bagelboy137/Bear-Necessities-/Mac Mini Setup/tools/cad-product-agent/production/ten-modules/visual/renders/BN-M06-alpha.png

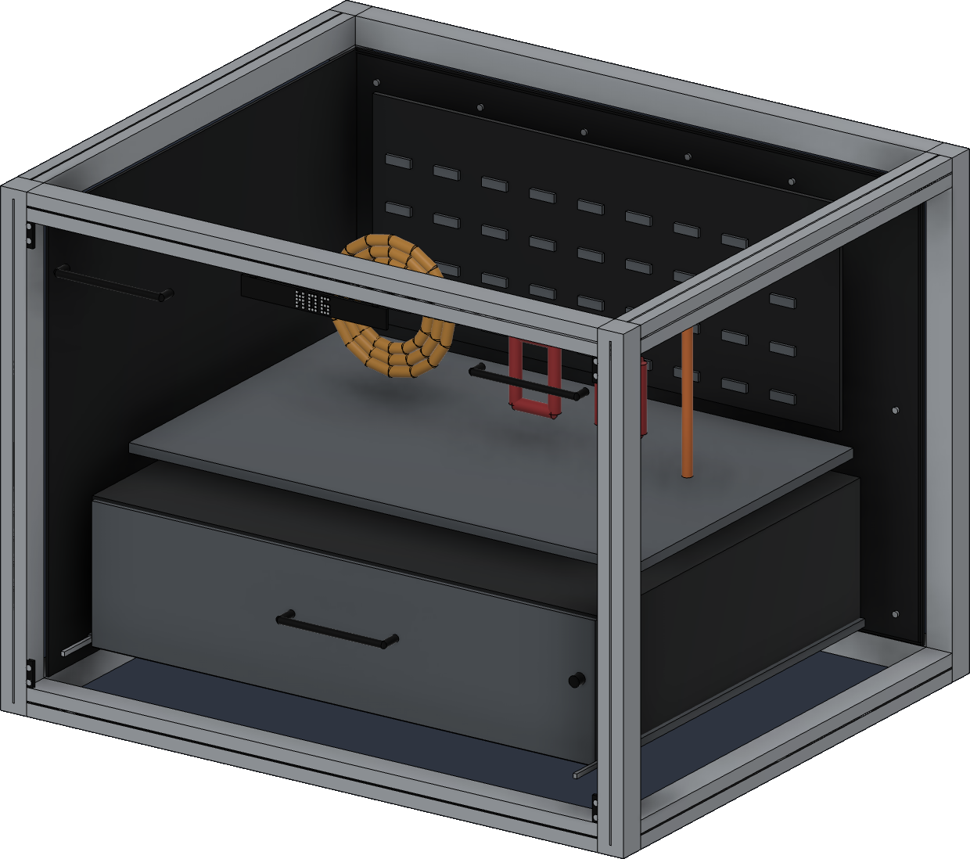
Mac Mini Setup/tools/cad-product-agent/production/ten-modules/visual/renders/BN-M06-alpha.png
