bagelboy137/Bear-Necessities-/Mac Mini Setup/tools/cad-product-agent/production/ten-modules/iterations/runs/design/design-06.attempt-1.raw.txt

```json
{
  "cycle_id": "design-06",
  "reviews": [
    {
      "module_id": "BN-M01",
      "verdict": "RETAIN",
      "proposal": "Retain the current design.",
      "rationale": "The module clearly communicates a secure stowed state with visible latches and restraints, as well as its deployed state with exposed burners and controls.",
      "evidence_ids": ["CURRENT-CAD", "FRAME-CONSTRAINTS"],
      "acceptance_check": "Check for visible latches and restraints in the stowed state.",
      "risk": "None"
    },
    {
      "module_id": "BN-M02",
      "verdict": "RETAIN",
      "proposal": "Retain the current design.",
      "rationale": "The module clearly communicates a secure stowed state with visible latches and restraints, as well as its deployed state with open drawers.",
      "evidence_ids": ["CURRENT-CAD", "FRAME-CONSTRAINTS"],
      "acceptance_check": "Check for visible latches and restraints in the stowed state.",
      "risk": "None"
    },
    {
      "module_id": "BN-M03",
      "verdict": "RETAIN",
      "proposal": "Retain the current design.",
      "rationale": "The module clearly communicates a secure stowed state with visible latches and restraints, as well as its deployed state with an open fridge lid.",
      "evidence_ids": ["CURRENT-CAD", "FRAME-CONSTRAINTS"],
      "acceptance_check": "Check for visible latches and restraints in the stowed state.",
      "risk": "None"
    },
    {
      "module_id": "BN-M04",
      "verdict": "RETAIN",
      "proposal": "Retain the current design.",
      "rationale": "The module clearly communicates a secure stowed state with visible latches and restraints, as well as its deployed state with an open basin.",
      "evidence_ids": ["CURRENT-CAD", "FRAME-CONSTRAINTS"],
      "acceptance_check": "Check for visible latches and restraints in the stowed state.",
      "risk": "None"
    },
    {
      "module_id": "BN-M05",
      "verdict": "RETAIN",
      "proposal": "Retain the current design.",
      "rationale": "The module clearly communicates a secure stowed state with visible latches and restraints, as well as its deployed state with an open spigot.",
      "evidence_ids": ["CURRENT-CAD", "FRAME-CONSTRAINTS"],
      "acceptance_check": "Check for visible latches and restraints in the stowed state.",
      "risk": "None"
    },
    {
      "module_id": "BN-M06",
      "verdict": "RETAIN",
      "proposal": "Retain the current design.",
      "rationale": "The module clearly communicates a secure stowed state with visible latches and restraints, as well as its deployed state with an open drawer.",
      "evidence_ids": ["CURRENT-CAD", "FRAME-CONSTRAINTS"],
      "acceptance_check": "Check for visible latches and restraints in the stowed state.",
      "risk": "None"
    },
    {
      "module_id": "BN-M07",
      "verdict": "RETAIN",
      "proposal": "Retain the current design.",
      "rationale": "The module clearly communicates a secure stowed state with visible latches and restraints, as well as its deployed state with open ports.",
      "evidence_ids": ["CURRENT-CAD", "FRAME-CONSTRAINTS"],
      "acceptance_check": "Check for visible latches and restraints in the stowed state.",
      "risk": "None"
    },
    {
      "module_id": "BN-M08",
      "verdict": "RETAIN",
      "proposal": "Retain the current design.",
      "rationale": "The module clearly communicates a secure stowed state with visible latches and restraints, as well as its deployed state with an open shower head.",
      "evidence_ids": ["CURRENT-CAD", "FRAME-CONSTRAINTS"],
      "acceptance_check": "Check for visible latches and restraints in the stowed state.",
      "risk": "None"
    },
    {
      "module_id": "BN-M09",
      "verdict": "RETAIN",
      "proposal": "Retain the current design.",
      "rationale": "The module clearly communicates a secure stowed state with visible latches and restraints, as well as its deployed state with an open worktop.",
      "evidence_ids": ["CURRENT-CAD", "FRAME-CONSTRAINTS"],
      "acceptance_check": "Check for visible latches and restraints in the stowed state.",
      "risk": "None"
    },
    {
      "module_id": "BN-M10",
      "verdict": "RETAIN",
      "proposal": "Retain the current design.",
      "rationale": "The module clearly communicates a secure stowed state with visible latches and restraints, as well as its deployed state with open furniture bags.",
      "evidence_ids": ["CURRENT-CAD", "FRAME-CONSTRAINTS"],
      "acceptance_check": "Check for visible latches and restraints in the stowed state.",
      "risk": "None"
    }
  ]
}
```
