bagelboy137/Bear-Necessities-/Mac Mini Setup/tools/cad-product-agent/production/ten-modules/iterations/runs/design/design-09.attempt-1.raw.txt

```json
{
  "cycle_id": "design-09",
  "reviews": [
    {
      "module_id": "BN-M01",
      "verdict": "RETAIN",
      "proposal": "Retain the current design.",
      "rationale": "The module maintains a distinct function as part of the silver-extrusion, dark-panel family.",
      "evidence_ids": ["CURRENT-CAD", "FRAME-CONSTRAINTS"],
      "acceptance_check": "Verify that the module adheres to the visual language constraints.",
      "risk": "None"
    },
    {
      "module_id": "BN-M02",
      "verdict": "RETAIN",
      "proposal": "Retain the current design.",
      "rationale": "The module maintains a distinct function as part of the silver-extrusion, dark-panel family.",
      "evidence_ids": ["CURRENT-CAD", "FRAME-CONSTRAINTS"],
      "acceptance_check": "Verify that the module adheres to the visual language constraints.",
      "risk": "None"
    },
    {
      "module_id": "BN-M03",
      "verdict": "RETAIN",
      "proposal": "Retain the current design.",
      "rationale": "The module maintains a distinct function as part of the silver-extrusion, dark-panel family.",
      "evidence_ids": ["CURRENT-CAD", "FRAME-CONSTRAINTS"],
      "acceptance_check": "Verify that the module adheres to the visual language constraints.",
      "risk": "None"
    },
    {
      "module_id": "BN-M04",
      "verdict": "RETAIN",
      "proposal": "Retain the current design.",
      "rationale": "The module maintains a distinct function as part of the silver-extrusion, dark-panel family.",
      "evidence_ids": ["CURRENT-CAD", "FRAME-CONSTRAINTS"],
      "acceptance_check": "Verify that the module adheres to the visual language constraints.",
      "risk": "None"
    },
    {
      "module_id": "BN-M05",
      "verdict": "RETAIN",
      "proposal": "Retain the current design.",
      "rationale": "The module maintains a distinct function as part of the silver-extrusion, dark-panel family.",
      "evidence_ids": ["CURRENT-CAD", "FRAME-CONSTRAINTS"],
      "acceptance_check": "Verify that the module adheres to the visual language constraints.",
      "risk": "None"
    },
    {
      "module_id": "BN-M06",
      "verdict": "RETAIN",
      "proposal": "Retain the current design.",
      "rationale": "The module maintains a distinct function as part of the silver-extrusion, dark-panel family.",
      "evidence_ids": ["CURRENT-CAD", "FRAME-CONSTRAINTS"],
      "acceptance_check": "Verify that the module adheres to the visual language constraints.",
      "risk": "None"
    },
    {
      "module_id": "BN-M07",
      "verdict": "RETAIN",
      "proposal": "Retain the current design.",
      "rationale": "The module maintains a distinct function as part of the silver-extrusion, dark-panel family.",
      "evidence_ids": ["CURRENT-CAD", "FRAME-CONSTRAINTS"],
      "acceptance_check": "Verify that the module adheres to the visual language constraints.",
      "risk": "None"
    },
    {
      "module_id": "BN-M08",
      "verdict": "RETAIN",
      "proposal": "Retain the current design.",
      "rationale": "The module maintains a distinct function as part of the silver-extrusion, dark-panel family.",
      "evidence_ids": ["CURRENT-CAD", "FRAME-CONSTRAINTS"],
      "acceptance_check": "Verify that the module adheres to the visual language constraints.",
      "risk": "None"
    },
    {
      "module_id": "BN-M09",
      "verdict": "RETAIN",
      "proposal": "Retain the current design.",
      "rationale": "The module maintains a distinct function as part of the silver-extrusion, dark-panel family.",
      "evidence_ids": ["CURRENT-CAD", "FRAME-CONSTRAINTS"],
      "acceptance_check": "Verify that the module adheres to the visual language constraints.",
      "risk": "None"
    },
    {
      "module_id": "BN-M10",
      "verdict": "RETAIN",
      "proposal": "Retain the current design.",
      "rationale": "The module maintains a distinct function as part of the silver-extrusion, dark-panel family.",
      "evidence_ids": ["CURRENT-CAD", "FRAME-CONSTRAINTS"],
      "acceptance_check": "Verify that the module adheres to the visual language constraints.",
      "risk": "None"
    }
  ]
}
```
