bagelboy137/Bear-Necessities-/Fusion CAD Agent/evals/tasks/01-plate.md

Write a Fusion Python API script that creates a 100 x 60 x 6 mm rectangular plate.
