bagelboy137/Bear-Necessities-/Fusion CAD Agent/evals/tasks/02-holes.md

Write a Fusion Python API script that creates a 100 x 60 x 6 mm rectangular plate, then adds four 8 mm through-holes, one 10 mm in from each corner measured to the hole centre.
