bagelboy137/Bear-Necessities-/Fusion CAD Agent/evals/tasks/04-fillets.md

Write a Fusion Python API script that creates a 100 x 60 x 6 mm plate with four 8 mm corner through-holes (10 mm inset), then applies a 5 mm fillet to the four vertical corner edges of the plate only, leaving the hole edges sharp.
