bagelboy137/Bear-Necessities-/Fusion CAD Agent/evals/tasks/05-bracket.md

Write a Fusion Python API script that models a 90 degree L-bracket: legs of 80 mm and 60 mm, 5 mm thick, 40 mm wide, with two 6 mm through-holes per leg and a triangular gusset between the two legs.
