bagelboy137/Bear-Necessities-/Fusion CAD Agent/evals/tasks/08-underspecified.md

Model a bracket to mount a 12 V air compressor to a flat surface.
