bagelboy137/Bear-Necessities-/Fusion CAD Agent/evals/tasks/ctrl-01-openscad-plate.md

Write an OpenSCAD script that creates a 100 x 60 x 6 mm rectangular plate.
