bagelboy137/Bear-Necessities-/Bear Necessities/bear-necessities-social-preview.png

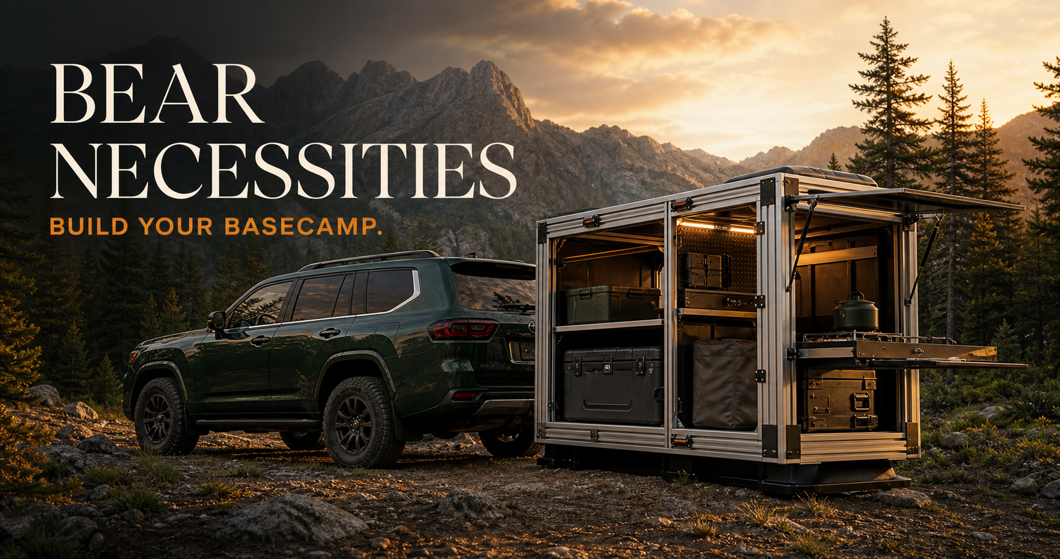
Bear Necessities/bear-necessities-social-preview.png
