bagelboy137/Bear-Necessities-/Bear Necessities/product/drawings/C-01-anchor-plate-FLAT.png

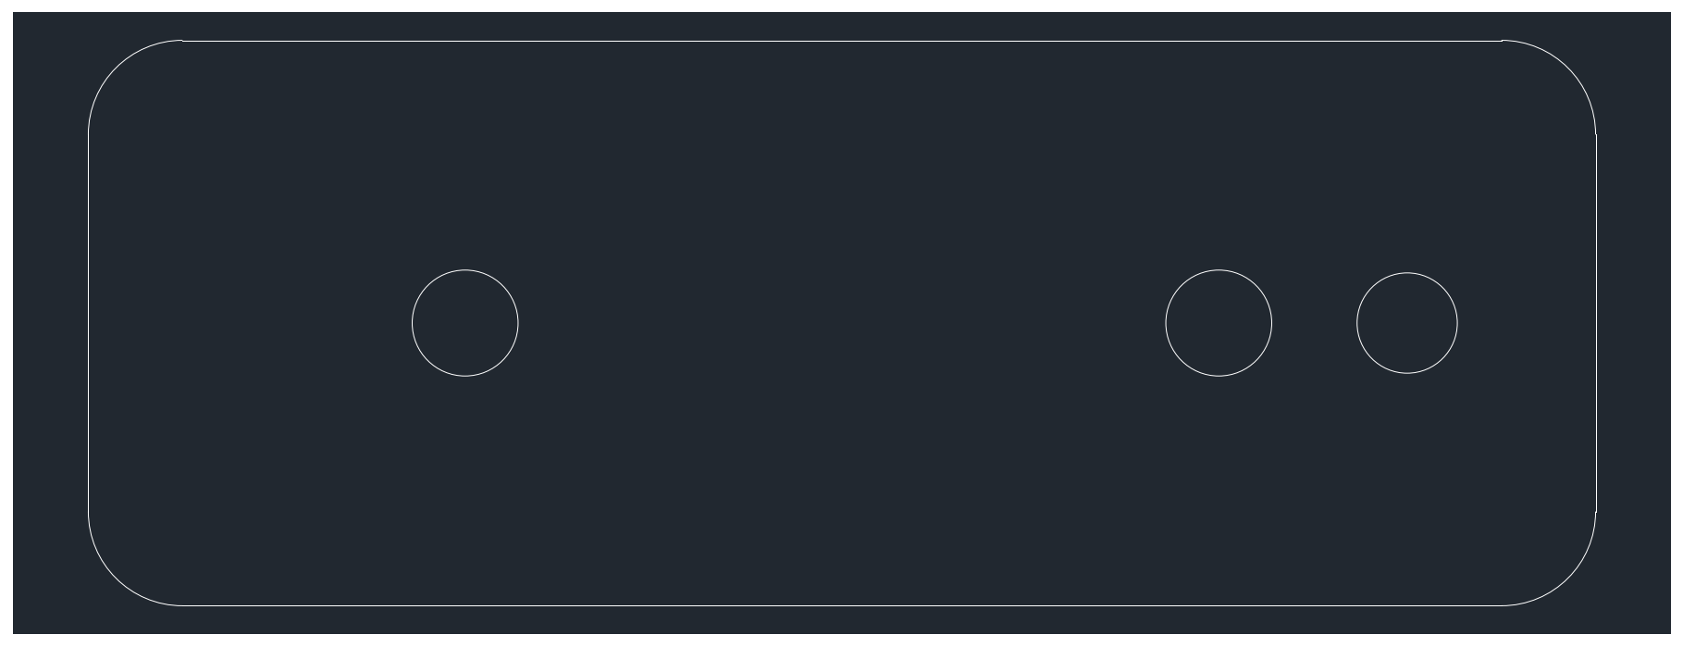
Bear Necessities/product/drawings/C-01-anchor-plate-FLAT.png
