bagelboy137/Bear-Necessities-/Bear Necessities/product/marketing/configurations/basecamp.png

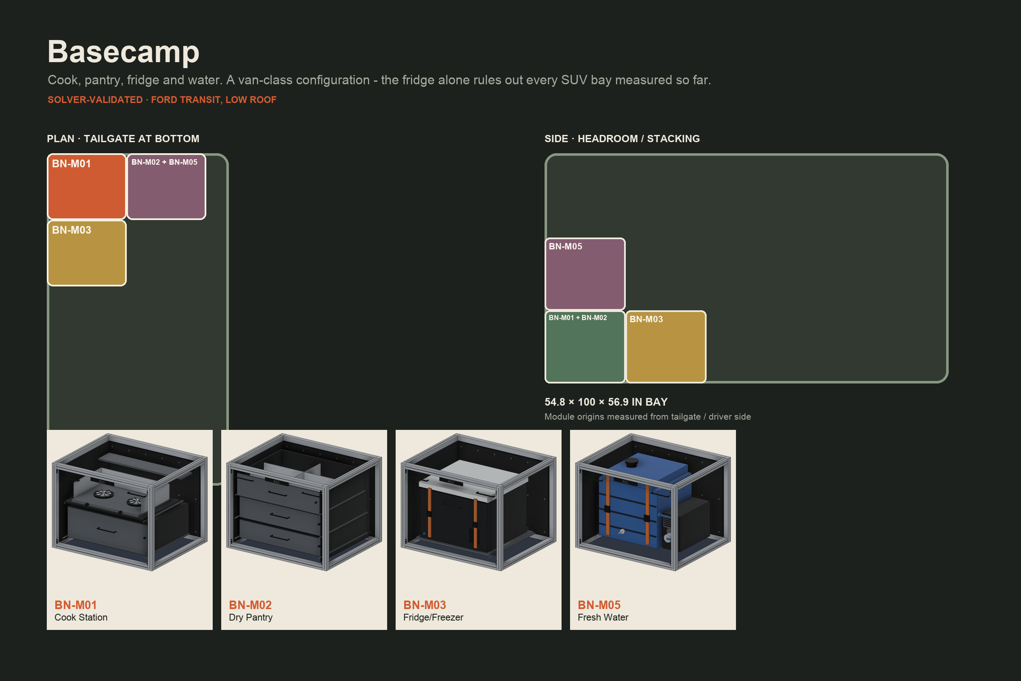
Bear Necessities/product/marketing/configurations/basecamp.png
