bagelboy137/Bear-Necessities-/Bear Necessities/product/marketing/configurations/expedition.png

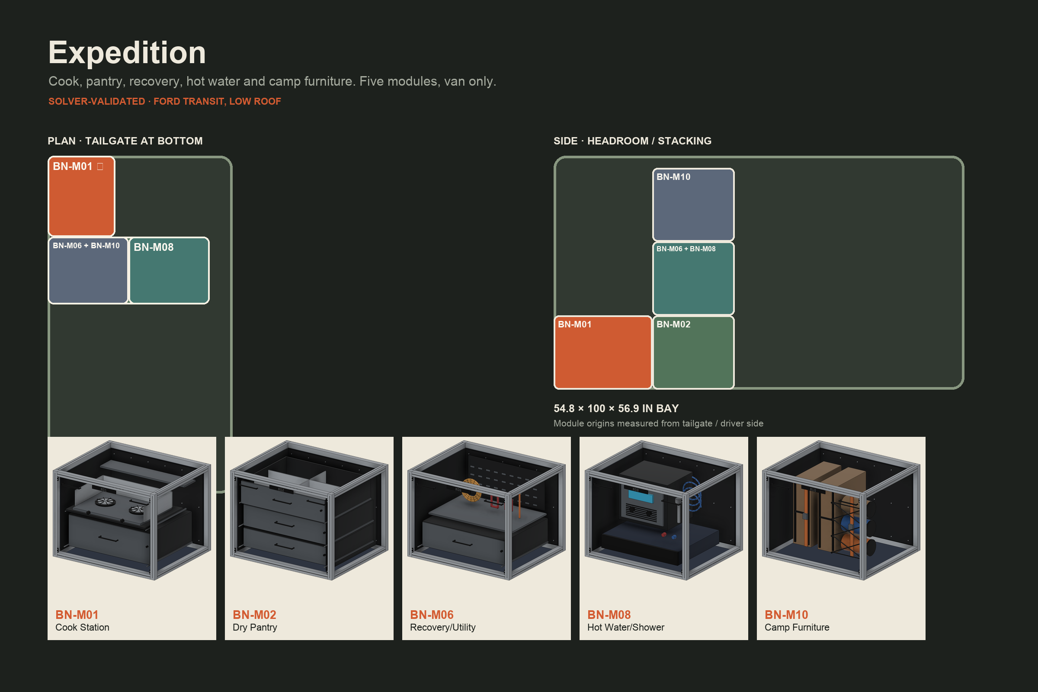
Bear Necessities/product/marketing/configurations/expedition.png
