bagelboy137/Bear-Necessities-/Bear Necessities/product/marketing/configurations/recovery-day.png

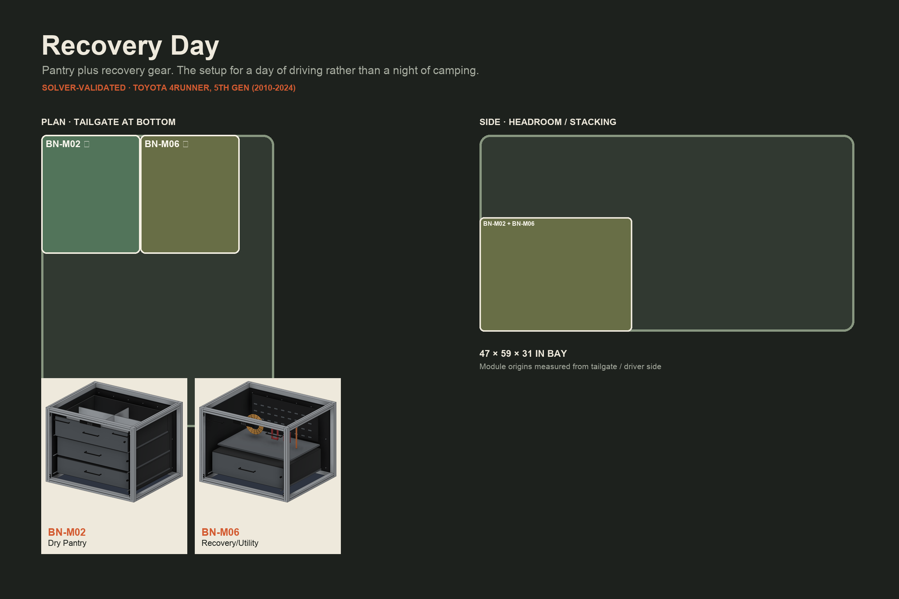
Bear Necessities/product/marketing/configurations/recovery-day.png
