bagelboy137/Bear-Necessities-/Bear Necessities/product/marketing/modules/BN-M01-alpha.png

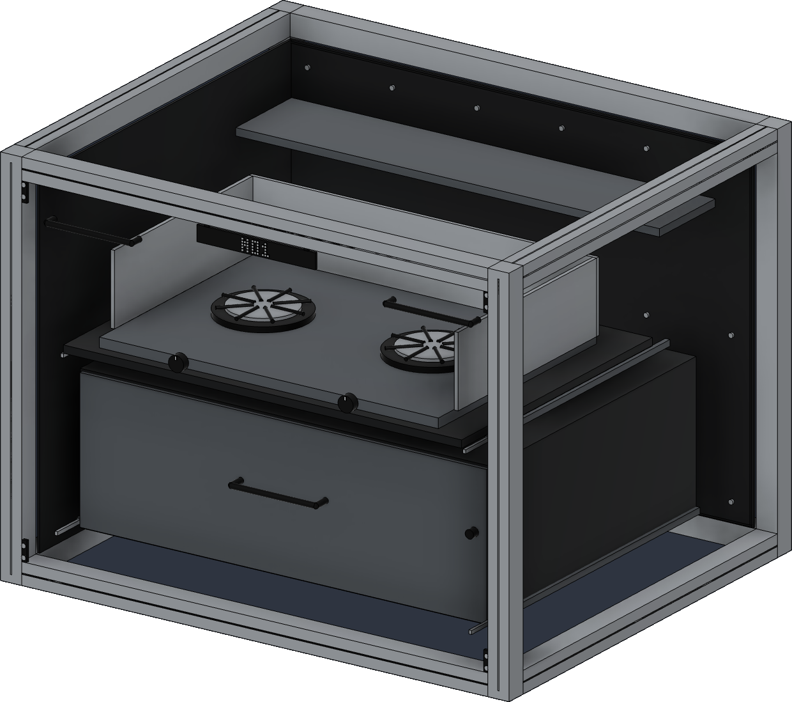
Bear Necessities/product/marketing/modules/BN-M01-alpha.png
