bagelboy137/Bear-Necessities-/Bear Necessities/product/marketing/modules/BN-M02-card.png

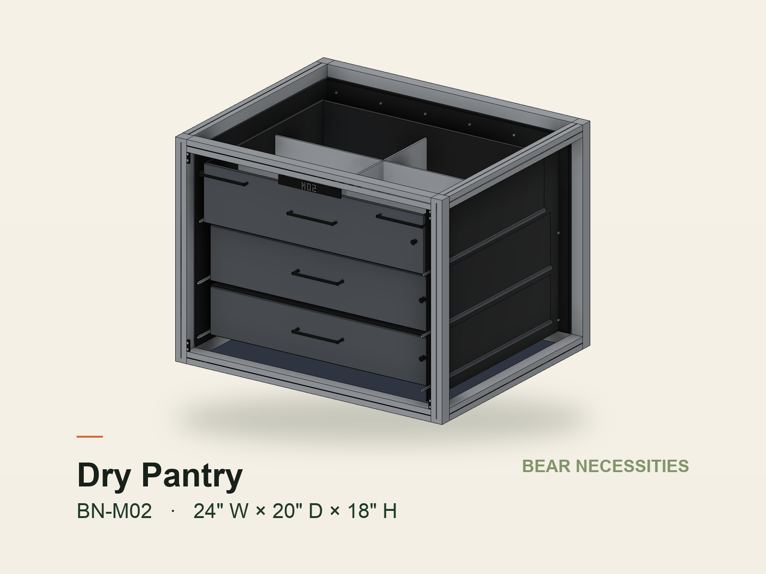
Bear Necessities/product/marketing/modules/BN-M02-card.png
