bagelboy137/Bear-Necessities-/Bear Necessities/product/marketing/modules/BN-M02-square.png

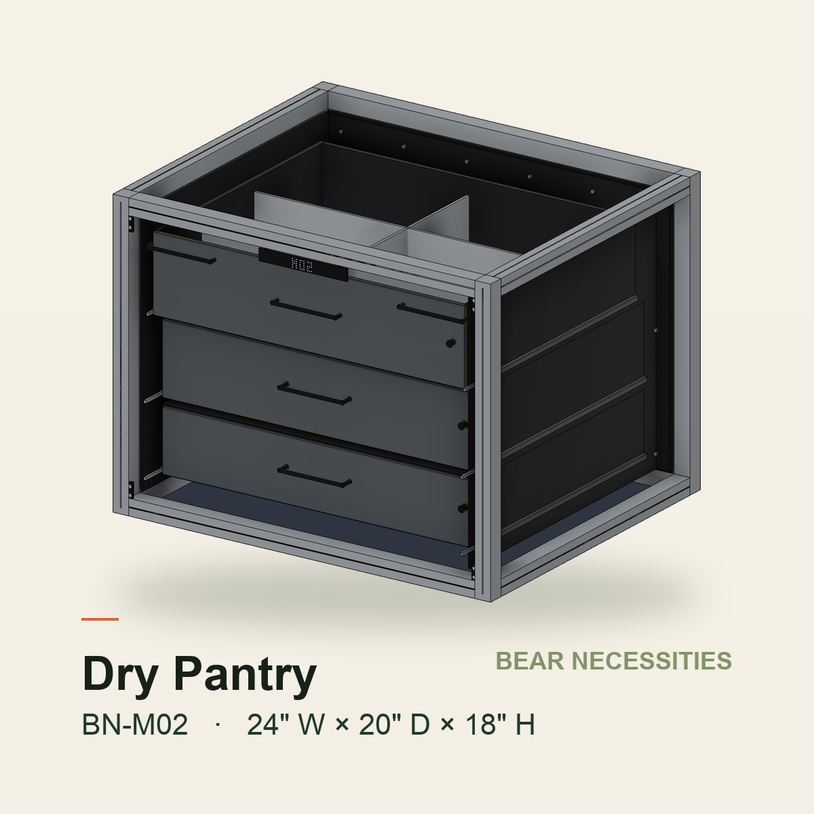
Bear Necessities/product/marketing/modules/BN-M02-square.png
