bagelboy137/Bear-Necessities-/Bear Necessities/product/marketing/modules/BN-M05-square.png

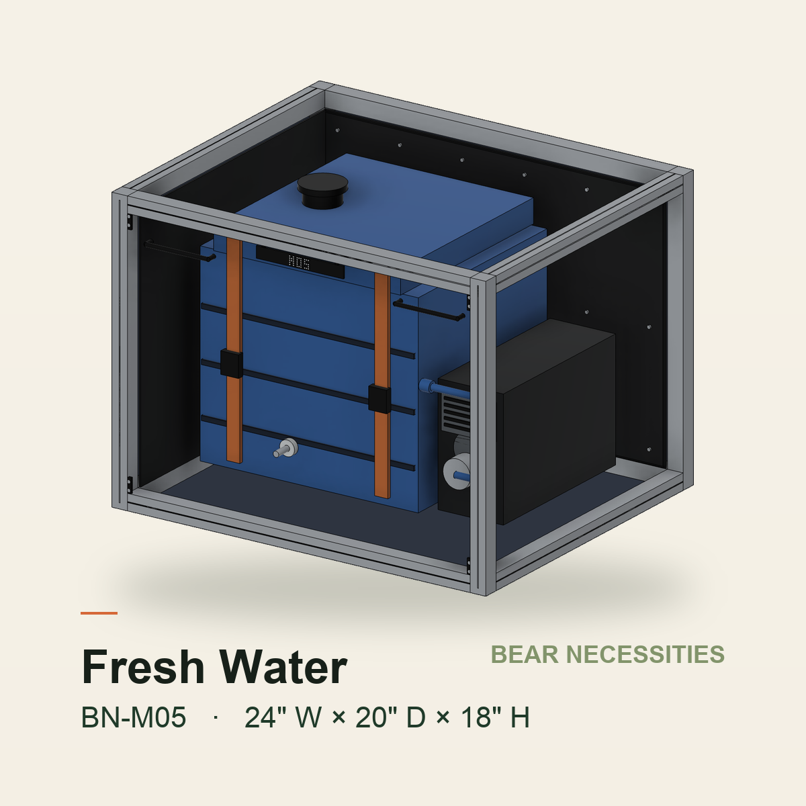
Bear Necessities/product/marketing/modules/BN-M05-square.png
