bagelboy137/Bear-Necessities-/Bear Necessities/product/marketing/modules/BN-M07-alpha.png

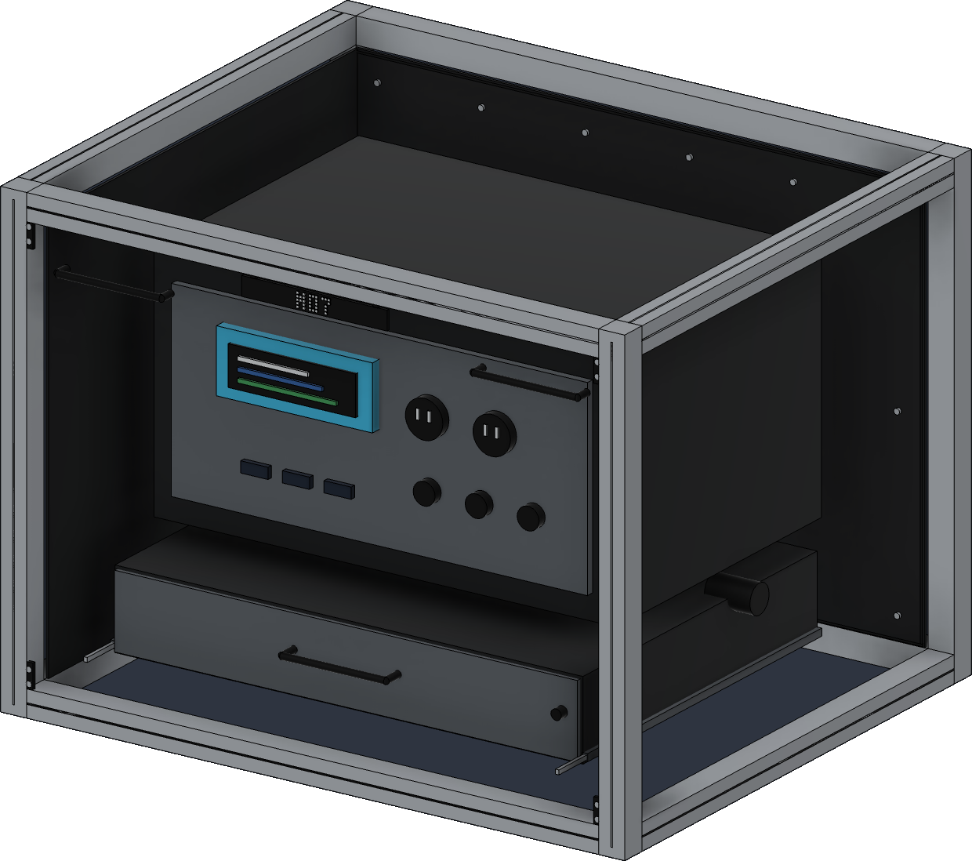
Bear Necessities/product/marketing/modules/BN-M07-alpha.png
