bagelboy137/Bear-Necessities-/Bear Necessities/product/marketing/modules/BN-M07-card.png

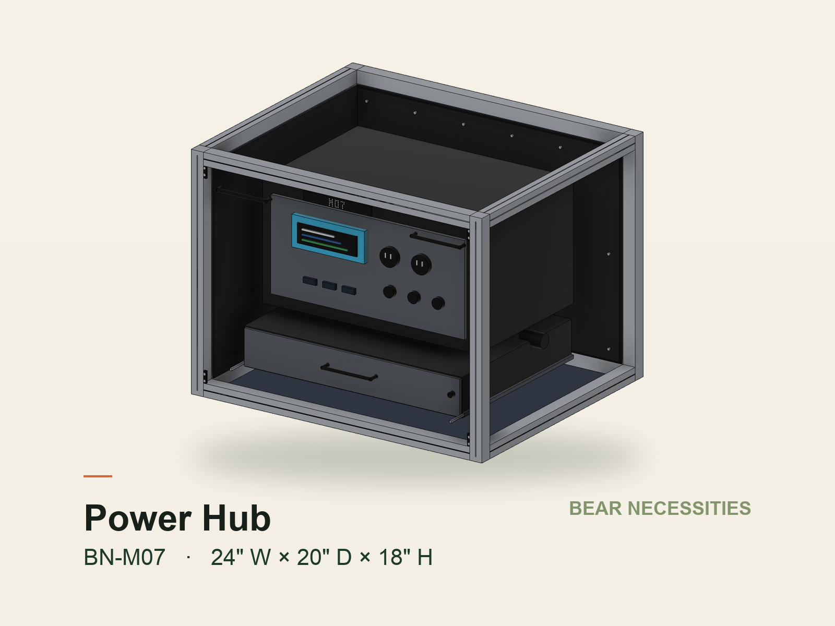
Bear Necessities/product/marketing/modules/BN-M07-card.png
