bagelboy137/Bear-Necessities-/Bear Necessities/product/marketing/modules/BN-M08-alpha.png

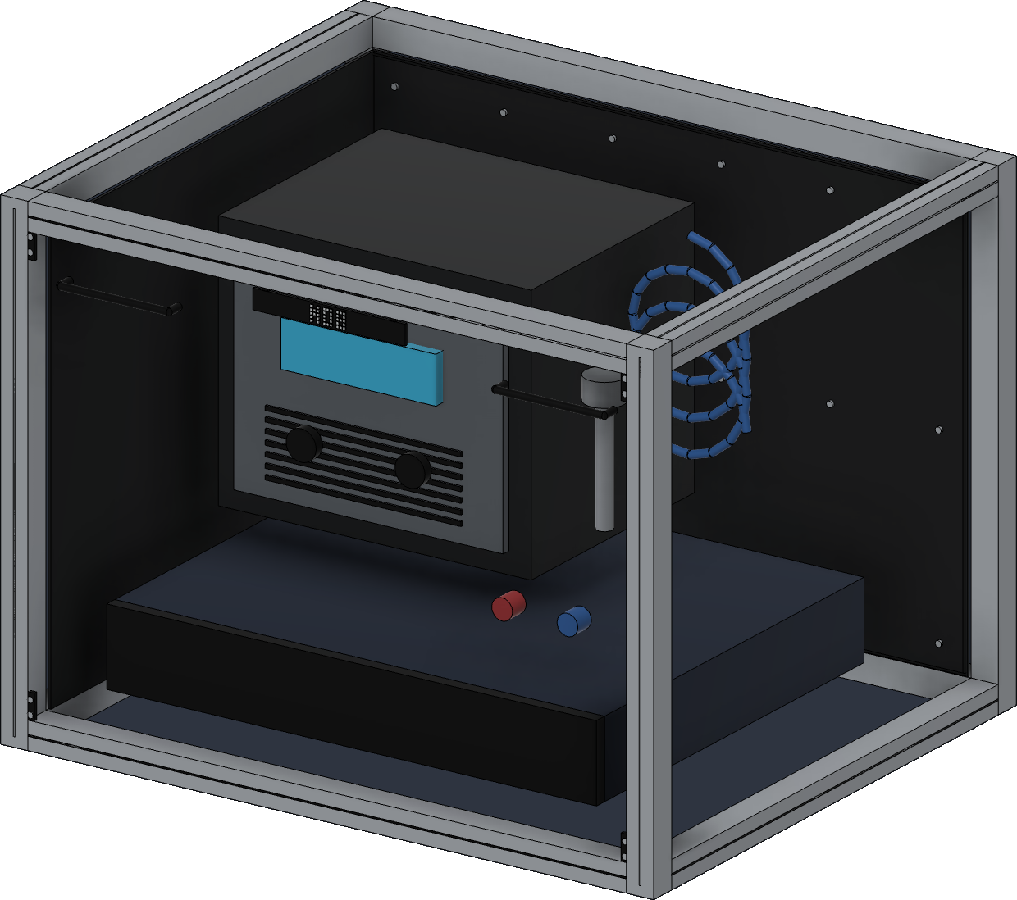
Bear Necessities/product/marketing/modules/BN-M08-alpha.png
