bagelboy137/Bear-Necessities-/Bear Necessities/product/marketing/modules/BN-M09-alpha.png

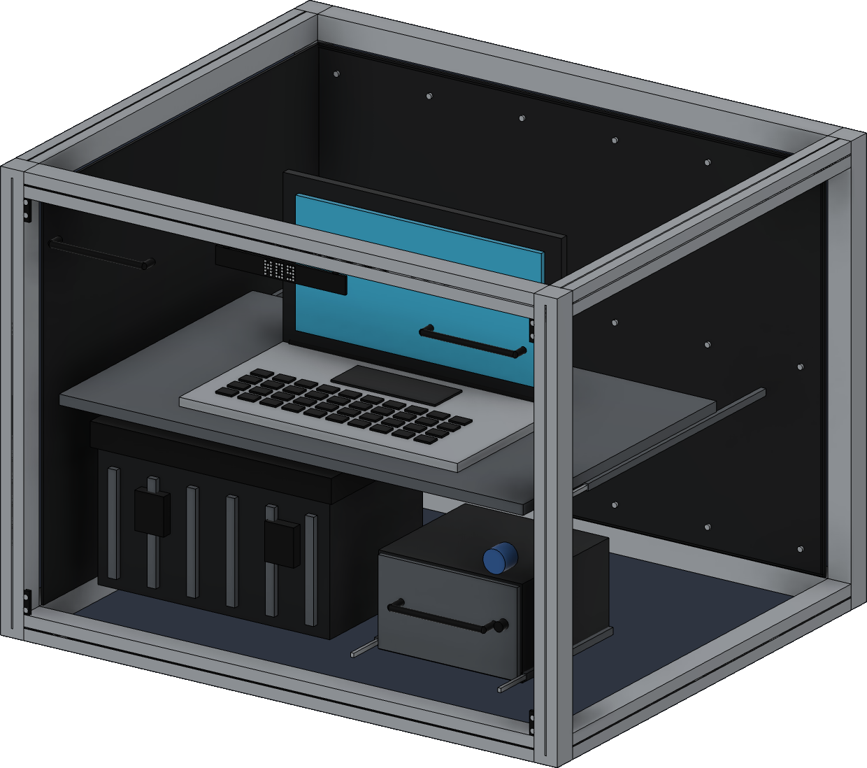
Bear Necessities/product/marketing/modules/BN-M09-alpha.png
