bagelboy137/Bear-Necessities-/Bear Necessities/product/marketing/modules/BN-M10-card.png

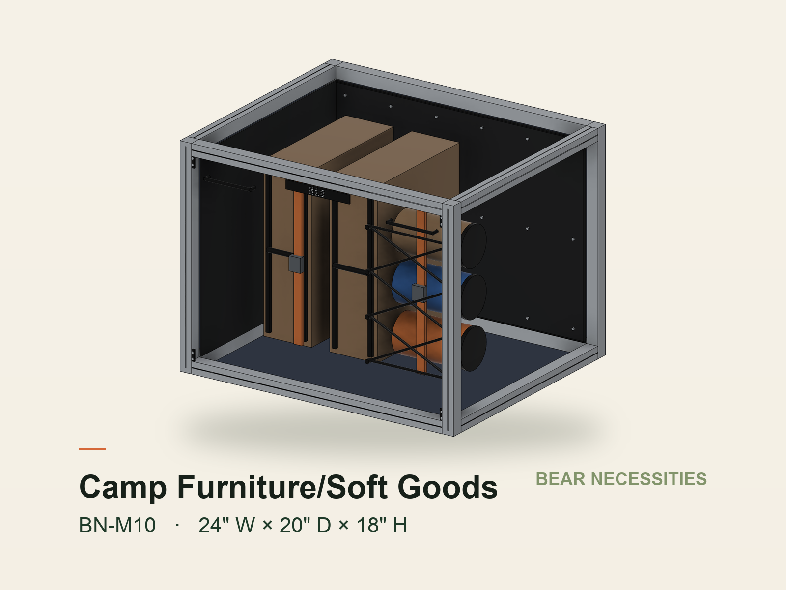
Bear Necessities/product/marketing/modules/BN-M10-card.png
