bagelboy137/Bear-Necessities-/Fusion CAD Agent/exports/bn-base-frame-fusion.png

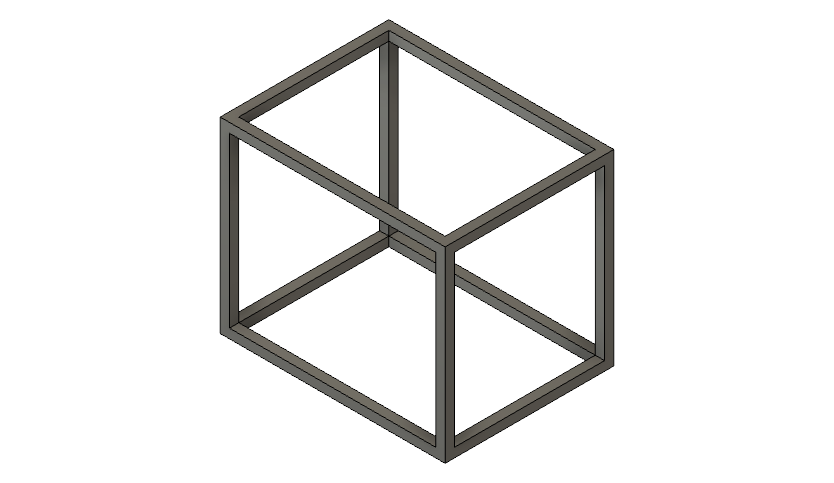
Fusion CAD Agent/exports/bn-base-frame-fusion.png
