bagelboy137/Bear-Necessities-/Fusion CAD Agent/exports/overland-base-frame-best.png

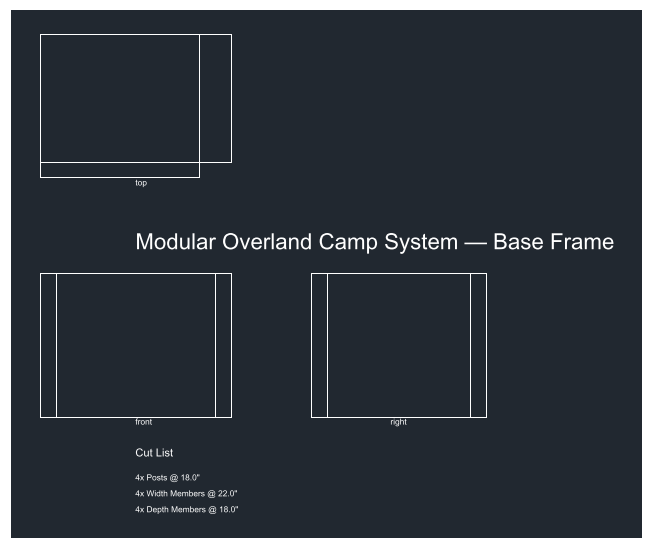
Fusion CAD Agent/exports/overland-base-frame-best.png
