bagelboy137/Bear-Necessities-/Fusion CAD Agent/exports/overland-base-frame.png

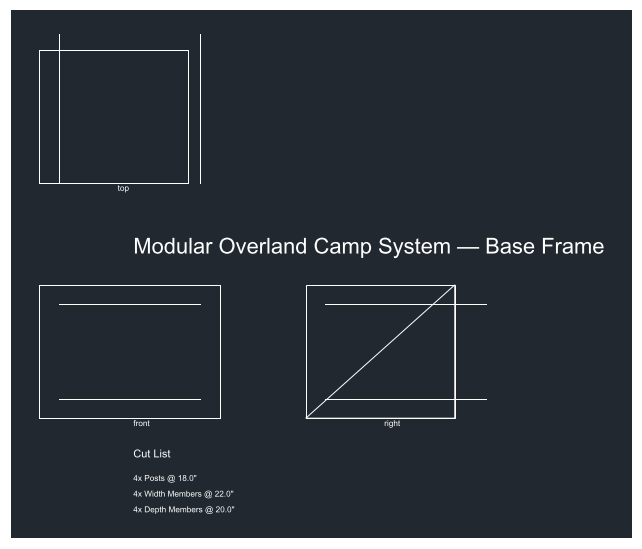
Fusion CAD Agent/exports/overland-base-frame.png
