bagelboy137/Bear-Necessities-/Mac Mini Setup/tools/cad-product-agent/production/ten-modules/SUPPLIER-READINESS.md

# Supplier and fulfillment readiness

Verified online 2026-08-25. “Orderable online” does not imply permission or
operational support for blind drop shipment to an end customer.

| Supplier/item | Online evidence | Current disposition |
|---|---|---|
| TNUTZ EX-1010 | Online configurable lengths include 18 and 22 inches; custom cutting/machining offered | Orderable; end-customer/blind-drop terms unverified |
| 80/20 1010-S | 1x1 smooth four-slot 6063-T6 extrusion, up to 242 inches | Orderable; higher apparent material/cut price than TNUTZ |
| 80/20 4132 | Online, 10 Series gusseted bracket; page specifies two 3393 mounting assemblies | Prototype orderable; production held for joint test |
| 80/20 3395 / TNUTZ AF-010 | Online internal anchor fastener requiring counterbore machining | Alternate only; quantity zero until joint architecture chosen |
| TNUTZ HAN-015-AL | Online handle with mounting hardware; only six shown in stock during review | Source/volume/load-rating hold |
| TNUTZ GAS-010-A | Online gasket for approximately 3/16-inch panels | Engineering hold until panel thickness is selected |
| TNUTZ BUM-010-TS | Online anti-skid 10 Series tread strip | Prototype orderable; vehicle-floor compatibility test required |
| Jetboil Genesis | Manufacturer online product with packed dimensions | Prototype orderable; reseller/drop-ship terms unverified |
| Engel MD-14F | Manufacturer page and dimensions verified, but page showed sold out | Availability hold |
| Reliance 9410-03R | Manufacturer page gives 7G dimensions and food-contact statements | Prototype orderable; reseller/drop-ship terms unverified |
| EcoFlow EF-RV-H02-1 | Manufacturer store and manual provide dimensions/electrical data | Prototype orderable; reseller/drop-ship terms unverified |
| Joolca HOTTAP V2 | US manufacturer store shows product and operating data | Prototype orderable; must be deployed outdoors |
| Pelican 1485 Air | Manufacturer product family lists compact Air case | Prototype orderable; exact configuration/SKU selection pending |

## Commercial questions to send each supplier

1. Will you ship individual orders directly to our retail customer using our
   packing slip, with no supplier invoice or marketing material?
2. Is account-level blind shipping supported, and is there a per-order fee?
3. Can our SKU and customer PO appear on labels and packing documents?
4. What cut-length tolerance, deburring, cosmetic standard and lot traceability
   apply to extrusion?
5. What are normal and peak-season lead times, stock feeds and substitution rules?
6. Who owns damage claims, returns, warranty triage and address corrections?
7. Are MAP, reseller authorization, territorial or marketplace restrictions involved?

Until these answers are accepted in writing, the BOM's online links support
prototype purchasing only—not a proven customer drop-ship operation.
