bagelboy137/Bear-Necessities-/Bear Necessities/product/bom/bom-single-module.csv

part_number | alt_part_number | description | vendor | qty | unit | notes | unit_price_usd
1010-S | EX-1010 | 1" x 1" smooth surface T-slotted profile, four open T-slots - CUT TO 18" | 80/20 Inc | 8 | pc | 4x Vertical corner post; 4x Depth rail
1010-S | EX-1010 | 1" x 1" smooth surface T-slotted profile, four open T-slots - CUT TO 22" | 80/20 Inc | 4 | pc | 4x Width rail
4132 |  | 10 Series 2 Hole Gusseted Inside Corner Bracket | 80/20 Inc | 24 | pc | 3 per corner x 8 corners. Gusseted (heavy duty) chosen over the 4108 LITE version because these modules carry a loaded fridge and are repeatedly lifted by their corners.
3395 |  | 10 Series 10-32 Standard Anchor Fastener (slide-in T-nut + cam + 10-32 SHCS) | 80/20 Inc | 48 | pc | 2 per bracket
