bagelboy137/Bear-Necessities-/Fusion CAD Agent/specs/reference/C-02-U-floor-bracket.step

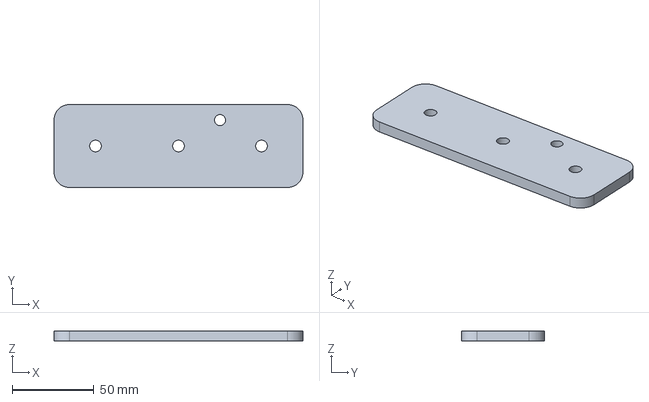
[picture p48: CAD file, 2026-09-25]
Fusion CAD Agent/specs/reference/C-02-U-floor-bracket.step
152.4 x 50.8 x 6.35 mm
