bagelboy137/Bear-Necessities-/Fusion CAD Agent/specs/reference/P05-spacer.step

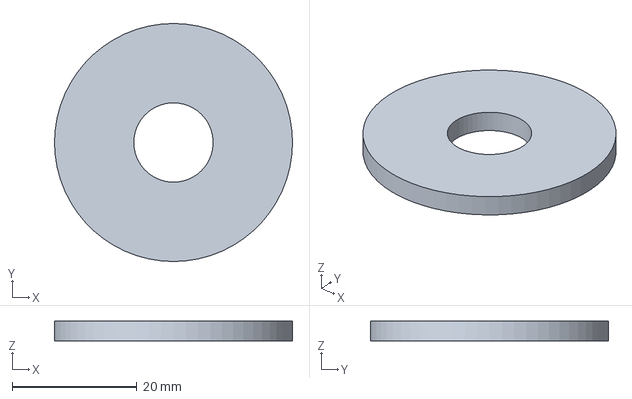
[picture p49: CAD file, 2026-09-25]
Fusion CAD Agent/specs/reference/P05-spacer.step
38.1 x 38.1 x 3.17 mm
