bagelboy137/Bear-Necessities-/Mac Mini Setup/tools/cad-product-agent/production/ten-modules/exports/BN-M01.step

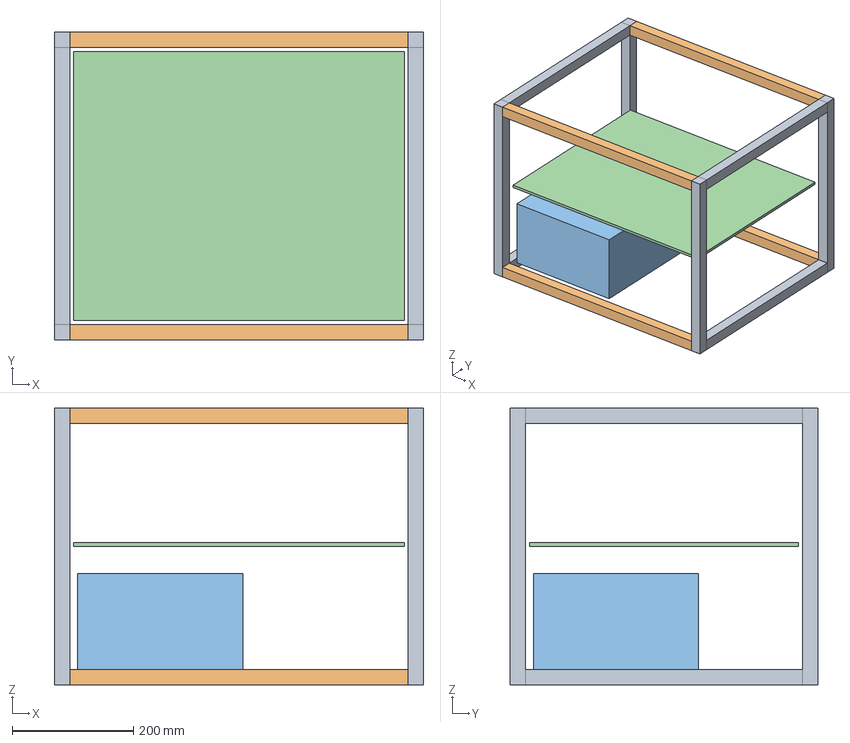
[picture p50: CAD file, 2026-09-25]
Mac Mini Setup/tools/cad-product-agent/production/ten-modules/exports/BN-M01.step
609.6 x 508.0 x 457.2 mm
