bagelboy137/Bear-Necessities-/Fusion CAD Agent/specs/reference/C-02-U-floor-bracket-authored.step

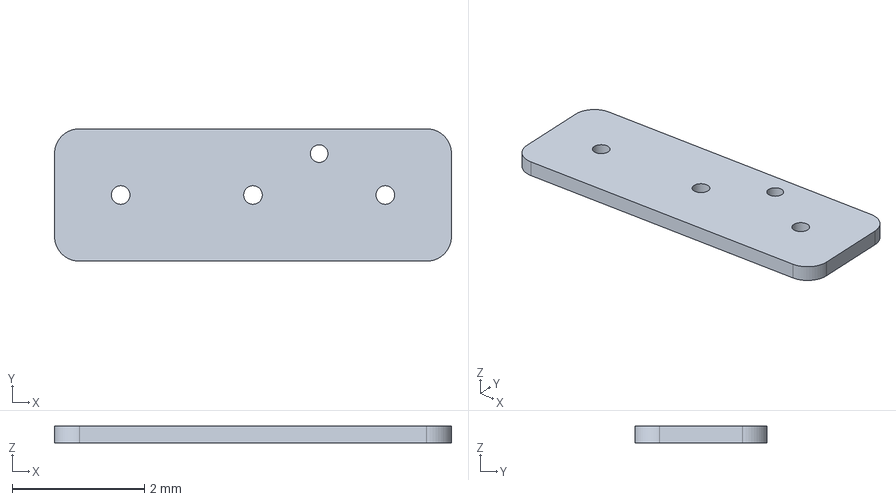
[picture p51: CAD file, 2026-09-25]
Fusion CAD Agent/specs/reference/C-02-U-floor-bracket-authored.step
6.00 x 2.00 x 0.25 mm
