bagelboy137/Bear-Necessities-/Mac Mini Setup/tools/cad-product-agent/production/ten-modules/exports/BN-M05.step

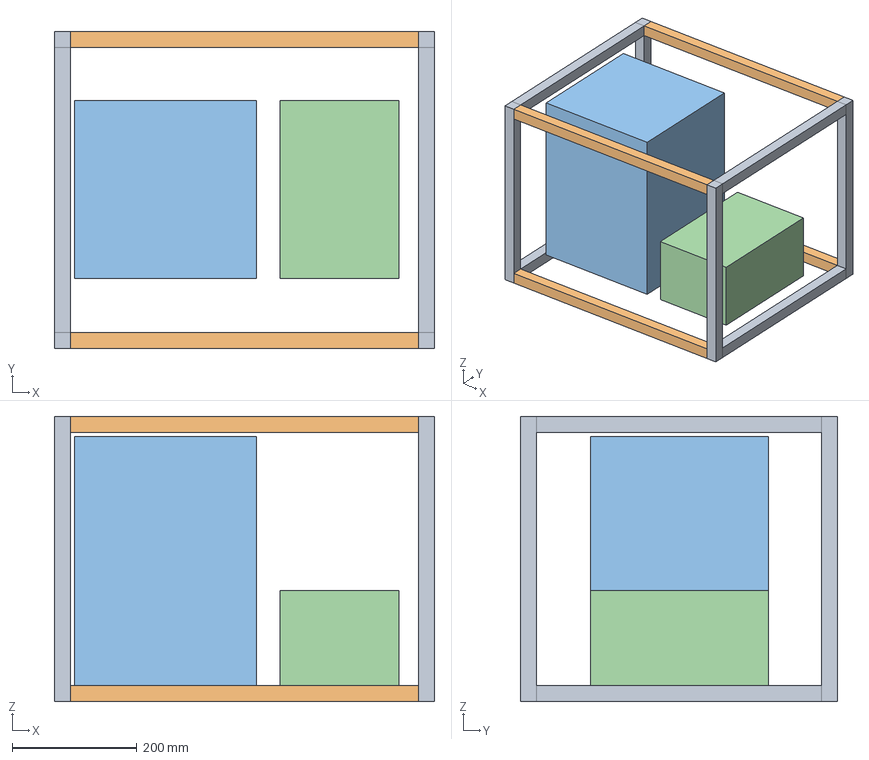
[picture p52: CAD file, 2026-09-25]
Mac Mini Setup/tools/cad-product-agent/production/ten-modules/exports/BN-M05.step
609.6 x 508.0 x 457.2 mm
