bagelboy137/Bear-Necessities-/Fusion CAD Agent/specs/reference/P05-spacer-authored.step

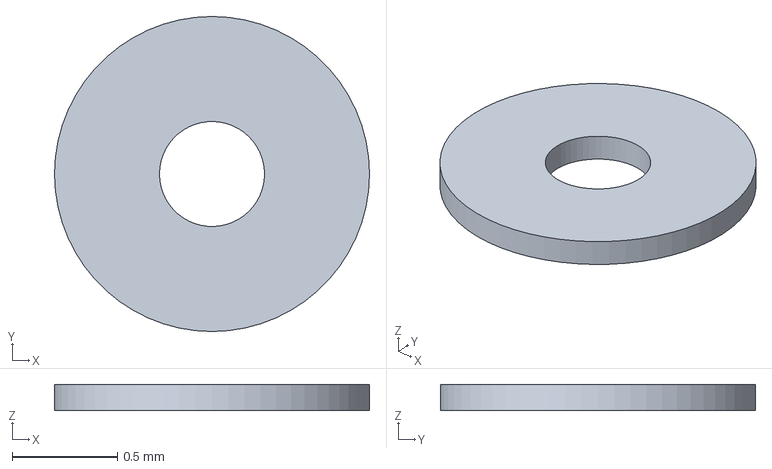
[picture p53: CAD file, 2026-09-25]
Fusion CAD Agent/specs/reference/P05-spacer-authored.step
1.50 x 1.50 x 0.125 mm
