bagelboy137/Bear-Necessities-/Fusion CAD Agent/specs/reference/P06-l-bracket-authored.step

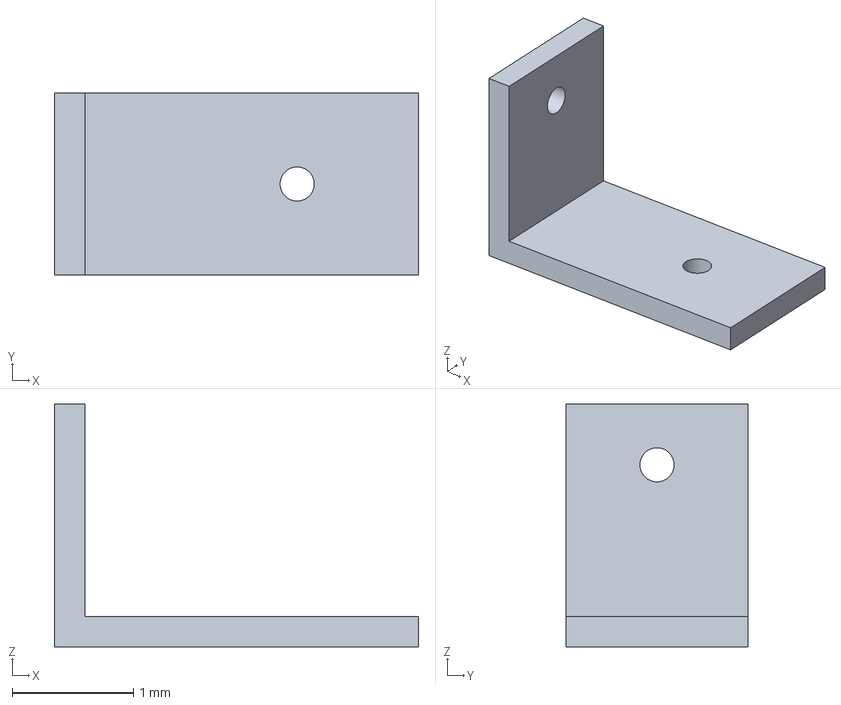
[picture p55: CAD file, 2026-09-25]
Fusion CAD Agent/specs/reference/P06-l-bracket-authored.step
3.00 x 1.50 x 2.00 mm
