bagelboy137/Bear-Necessities-/Fusion CAD Agent/specs/reference/P06-l-bracket.step

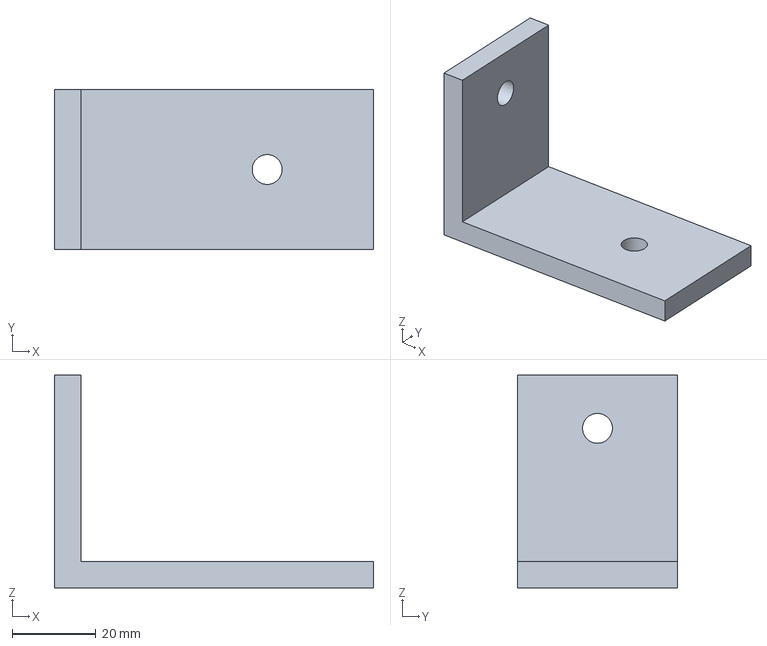
[picture p57: CAD file, 2026-09-25]
Fusion CAD Agent/specs/reference/P06-l-bracket.step
76.2 x 38.1 x 50.8 mm
