bagelboy137/Bear-Necessities-/Fusion CAD Agent/specs/reference/P01-plate.step

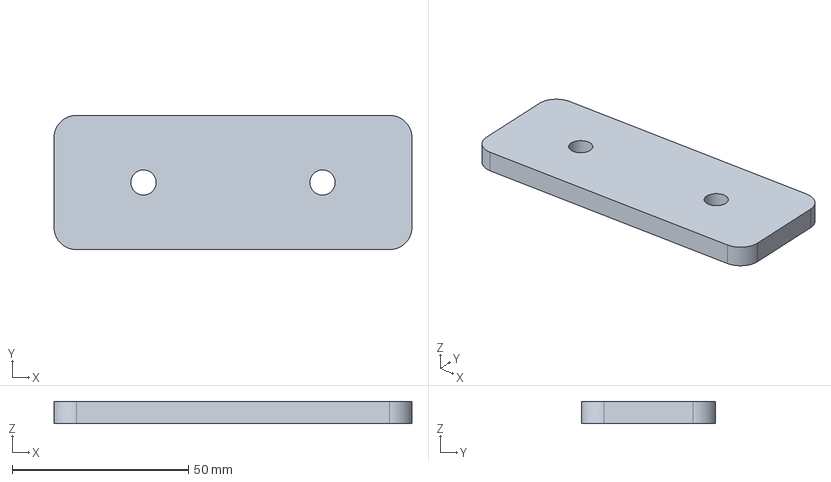
[picture p59: CAD file, 2026-09-25]
Fusion CAD Agent/specs/reference/P01-plate.step
101.6 x 38.1 x 6.35 mm
