bagelboy137/Bear-Necessities-/Mac Mini Setup/tools/cad-product-agent/production/ten-modules/iterations/runs/manufacturing/manufacturing-01.attempt-1.raw.txt

```json
{
  "cycle_id": "manufacturing-01",
  "reviews": [
    {
      "module_id": "BN-M01",
      "verdict": "RETAIN",
      "proposal": "Retain the current design.",
      "rationale": "The module adheres to the fixed 18/22-inch cut list and uses the released 1-inch 10-Series extrusion family.",
      "evidence_ids": ["CURRENT-CAD", "FRAME-CONSTRAINTS", "TNUTZ-EX1010-18", "TNUTZ-EX1010-22"],
      "acceptance_check": "Verify that all components are within the 18/22-inch cut list and use 10-Series extrusions.",
      "risk": "None"
    },
    {
      "module_id": "BN-M02",
      "verdict": "RETAIN",
      "proposal": "Retain the current design.",
      "rationale": "The module adheres to the fixed 18/22-inch cut list and uses the released 1-inch 10-Series extrusion family.",
      "evidence_ids": ["CURRENT-CAD", "FRAME-CONSTRAINTS", "TNUTZ-EX1010-18", "TNUTZ-EX1010-22"],
      "acceptance_check": "Verify that all components are within the 18/22-inch cut list and use 10-Series extrusions.",
      "risk": "None"
    },
    {
      "module_id": "BN-M03",
      "verdict": "RETAIN",
      "proposal": "Retain the current design.",
      "rationale": "The module adheres to the fixed 18/22-inch cut list and uses the released 1-inch 10-Series extrusion family.",
      "evidence_ids": ["CURRENT-CAD", "FRAME-CONSTRAINTS", "TNUTZ-EX1010-18", "TNUTZ-EX1010-22"],
      "acceptance_check": "Verify that all components are within the 18/22-inch cut list and use 10-Series extrusions.",
      "risk": "None"
    },
    {
      "module_id": "BN-M04",
      "verdict": "RETAIN",
      "proposal": "Retain the current design.",
      "rationale": "The module adheres to the fixed 18/22-inch cut list and uses the released 1-inch 10-Series extrusion family.",
      "evidence_ids": ["CURRENT-CAD", "FRAME-CONSTRAINTS", "TNUTZ-EX1010-18", "TNUTZ-EX1010-22"],
      "acceptance_check": "Verify that all components are within the 18/22-inch cut list and use 10-Series extrusions.",
      "risk": "None"
    },
    {
      "module_id": "BN-M05",
      "verdict": "RETAIN",
      "proposal": "Retain the current design.",
      "rationale": "The module adheres to the fixed 18/22-inch cut list and uses the released 1-inch 10-Series extrusion family.",
      "evidence_ids": ["CURRENT-CAD", "FRAME-CONSTRAINTS", "TNUTZ-EX1010-18", "TNUTZ-EX1010-22"],
      "acceptance_check": "Verify that all components are within the 18/22-inch cut list and use 10-Series extrusions.",
      "risk": "None"
    },
    {
      "module_id": "BN-M06",
      "verdict": "RETAIN",
      "proposal": "Retain the current design.",
      "rationale": "The module adheres to the fixed 18/22-inch cut list and uses the released 1-inch 10-Series extrusion family.",
      "evidence_ids": ["CURRENT-CAD", "FRAME-CONSTRAINTS", "TNUTZ-EX1010-18", "TNUTZ-EX1010-22"],
      "acceptance_check": "Verify that all components are within the 18/22-inch cut list and use 10-Series extrusions.",
      "risk": "None"
    },
    {
      "module_id": "BN-M07",
      "verdict": "RETAIN",
      "proposal": "Retain the current design.",
      "rationale": "The module adheres to the fixed 18/22-inch cut list and uses the released 1-inch 10-Series extrusion family.",
      "evidence_ids": ["CURRENT-CAD", "FRAME-CONSTRAINTS", "TNUTZ-EX1010-18", "TNUTZ-EX1010-22"],
      "acceptance_check": "Verify that all components are within the 18/22-inch cut list and use 10-Series extrusions.",
      "risk": "None"
    },
    {
      "module_id": "BN-M08",
      "verdict": "RETAIN",
      "proposal": "Retain the current design.",
      "rationale": "The module adheres to the fixed 18/22-inch cut list and uses the released 1-inch 10-Series extrusion family.",
      "evidence_ids": ["CURRENT-CAD", "FRAME-CONSTRAINTS", "TNUTZ-EX1010-18", "TNUTZ-EX1010-22"],
      "acceptance_check": "Verify that all components are within the 18/22-inch cut list and use 10-Series extrusions.",
      "risk": "None"
    },
    {
      "module_id": "BN-M09",
      "verdict": "RETAIN",
      "proposal": "Retain the current design.",
      "rationale": "The module adheres to the fixed 18/22-inch cut list and uses the released 1-inch 10-Series extrusion family.",
      "evidence_ids": ["CURRENT-CAD", "FRAME-CONSTRAINTS", "TNUTZ-EX1010-18", "TNUTZ-EX1010-22"],
      "acceptance_check": "Verify that all components are within the 18/22-inch cut list and use 10-Series extrusions.",
      "risk": "None"
    },
    {
      "module_id": "BN-M10",
      "verdict": "RETAIN",
      "proposal": "Retain the current design.",
      "rationale": "The module adheres to the fixed 18/22-inch cut list and uses the released 1-inch 10-Series extrusion family.",
      "evidence_ids": ["CURRENT-CAD", "FRAME-CONSTRAINTS", "TNUTZ-EX1010-18", "TNUTZ-EX1010-22"],
      "acceptance_check": "Verify that all components are within the 18/22-inch cut list and use 10-Series extrusions.",
      "risk": "None"
    }
  ]
}
```
