bagelboy137/Bear-Necessities-/Mac Mini Setup/tools/cad-product-agent/production/ten-modules/iterations/runs/manufacturing/manufacturing-02.attempt-1.raw.txt

```json
{
  "cycle_id": "manufacturing-02",
  "reviews": [
    {
      "module_id": "BN-M01",
      "verdict": "RETAIN",
      "proposal": "Retain the current design.",
      "rationale": "The unique cut lengths and custom part count are essential for the cook station's functionality.",
      "evidence_ids": ["CURRENT-CAD", "FRAME-CONSTRAINTS", "TAP-HYPACT-PANEL", "TNUTZ-GAS010A"],
      "acceptance_check": "Verify that the cook station maintains its current design and functionality.",
      "risk": "None"
    },
    {
      "module_id": "BN-M02",
      "verdict": "RETAIN",
      "proposal": "Retain the current design.",
      "rationale": "The unique cut lengths and custom part count are essential for the dry pantry's functionality.",
      "evidence_ids": ["CURRENT-CAD", "FRAME-CONSTRAINTS", "RUBBERMAID-FG350700WHT", "TAP-HYPACT-PANEL"],
      "acceptance_check": "Verify that the dry pantry maintains its current design and functionality.",
      "risk": "None"
    },
    {
      "module_id": "BN-M03",
      "verdict": "RETAIN",
      "proposal": "Retain the current design.",
      "rationale": "The unique cut lengths and custom part count are essential for the fridge freezer's functionality.",
      "evidence_ids": ["CURRENT-CAD", "FRAME-CONSTRAINTS", "ENGEL-MD14", "TAP-HYPACT-PANEL"],
      "acceptance_check": "Verify that the fridge freezer maintains its current design and functionality.",
      "risk": "None"
    },
    {
      "module_id": "BN-M04",
      "verdict": "RETAIN",
      "proposal": "Retain the current design.",
      "rationale": "The unique cut lengths and custom part count are essential for the sink wash's functionality.",
      "evidence_ids": ["CURRENT-CAD", "FRAME-CONSTRAINTS", "DOMETIC-VA8005", "TAP-HYPACT-PANEL"],
      "acceptance_check": "Verify that the sink wash maintains its current design and functionality.",
      "risk": "None"
    },
    {
      "module_id": "BN-M05",
      "verdict": "RETAIN",
      "proposal": "Retain the current design.",
      "rationale": "The unique cut lengths and custom part count are essential for the fresh water's functionality.",
      "evidence_ids": ["CURRENT-CAD", "FRAME-CONSTRAINTS", "RELIANCE-AQUATAINER-7G", "TAP-HYPACT-PANEL"],
      "acceptance_check": "Verify that the fresh water maintains its current design and functionality.",
      "risk": "None"
    },
    {
      "module_id": "BN-M06",
      "verdict": "RETAIN",
      "proposal": "Retain the current design.",
      "rationale": "The unique cut lengths and custom part count are essential for the recovery utility's functionality.",
      "evidence_ids": ["CURRENT-CAD", "FRAME-CONSTRAINTS", "PELICAN-1450", "TAP-HYPACT-PANEL"],
      "acceptance_check": "Verify that the recovery utility maintains its current design and functionality.",
      "risk": "None"
    },
    {
      "module_id": "BN-M07",
      "verdict": "RETAIN",
      "proposal": "Retain the current design.",
      "rationale": "The unique cut lengths and custom part count are essential for the power hub's functionality.",
      "evidence_ids": ["CURRENT-CAD", "FRAME-CONSTRAINTS", "ECOFLOW-RIVER3-PLUS", "TAP-HYPACT-PANEL"],
      "acceptance_check": "Verify that the power hub maintains its current design and functionality.",
      "risk": "None"
    },
    {
      "module_id": "BN-M08",
      "verdict": "RETAIN",
      "proposal": "Retain the current design.",
      "rationale": "The unique cut lengths and custom part count are essential for the hot water shower's functionality.",
      "evidence_ids": ["CURRENT-CAD", "FRAME-CONSTRAINTS", "JOOLCA-HOTTAP-V2", "TAP-HYPACT-PANEL"],
      "acceptance_check": "Verify that the hot water shower maintains its current design and functionality.",
      "risk": "None"
    },
    {
      "module_id": "BN-M09",
      "verdict": "RETAIN",
      "proposal": "Retain the current design.",
      "rationale": "The unique cut lengths and custom part count are essential for the field office camera's functionality.",
      "evidence_ids": ["CURRENT-CAD", "FRAME-CONSTRAINTS", "PELICAN-1485", "TAP-HYPACT-PANEL"],
      "acceptance_check": "Verify that the field office camera maintains its current design and functionality.",
      "risk": "None"
    },
    {
      "module_id": "BN-M10",
      "verdict": "RETAIN",
      "proposal": "Retain the current design.",
      "rationale": "The unique cut lengths and custom part count are essential for the camp furniture soft goods' functionality.",
      "evidence_ids": ["CURRENT-CAD", "FRAME-CONSTRAINTS", "HELINOX-CHAIR-ONE", "TAP-HYPACT-PANEL"],
      "acceptance_check": "Verify that the camp furniture soft goods maintains its current design and functionality.",
      "risk": "None"
    }
  ]
}
```
