bagelboy137/Bear-Necessities-/Mac Mini Setup/tools/cad-product-agent/production/ten-modules/iterations/runs/manufacturing/manufacturing-03.attempt-1.raw.txt

```json
{
  "cycle_id": "manufacturing-03",
  "reviews": [
    {
      "module_id": "BN-M01",
      "verdict": "RETAIN",
      "proposal": "Retain the current design.",
      "rationale": "The module uses a compatible bracket-and-fastener architecture for frame joints, adhering to the specified criteria.",
      "evidence_ids": ["CURRENT-CAD"],
      "acceptance_check": "Visual inspection of the module's frame joints.",
      "risk": "None"
    },
    {
      "module_id": "BN-M02",
      "verdict": "RETAIN",
      "proposal": "Retain the current design.",
      "rationale": "The module uses a compatible bracket-and-fastener architecture for frame joints, adhering to the specified criteria.",
      "evidence_ids": ["CURRENT-CAD"],
      "acceptance_check": "Visual inspection of the module's frame joints.",
      "risk": "None"
    },
    {
      "module_id": "BN-M03",
      "verdict": "RETAIN",
      "proposal": "Retain the current design.",
      "rationale": "The module uses a compatible bracket-and-fastener architecture for frame joints, adhering to the specified criteria.",
      "evidence_ids": ["CURRENT-CAD"],
      "acceptance_check": "Visual inspection of the module's frame joints.",
      "risk": "None"
    },
    {
      "module_id": "BN-M04",
      "verdict": "RETAIN",
      "proposal": "Retain the current design.",
      "rationale": "The module uses a compatible bracket-and-fastener architecture for frame joints, adhering to the specified criteria.",
      "evidence_ids": ["CURRENT-CAD"],
      "acceptance_check": "Visual inspection of the module's frame joints.",
      "risk": "None"
    },
    {
      "module_id": "BN-M05",
      "verdict": "RETAIN",
      "proposal": "Retain the current design.",
      "rationale": "The module uses a compatible bracket-and-fastener architecture for frame joints, adhering to the specified criteria.",
      "evidence_ids": ["CURRENT-CAD"],
      "acceptance_check": "Visual inspection of the module's frame joints.",
      "risk": "None"
    },
    {
      "module_id": "BN-M06",
      "verdict": "RETAIN",
      "proposal": "Retain the current design.",
      "rationale": "The module uses a compatible bracket-and-fastener architecture for frame joints, adhering to the specified criteria.",
      "evidence_ids": ["CURRENT-CAD"],
      "acceptance_check": "Visual inspection of the module's frame joints.",
      "risk": "None"
    },
    {
      "module_id": "BN-M07",
      "verdict": "RETAIN",
      "proposal": "Retain the current design.",
      "rationale": "The module uses a compatible bracket-and-fastener architecture for frame joints, adhering to the specified criteria.",
      "evidence_ids": ["CURRENT-CAD"],
      "acceptance_check": "Visual inspection of the module's frame joints.",
      "risk": "None"
    },
    {
      "module_id": "BN-M08",
      "verdict": "RETAIN",
      "proposal": "Retain the current design.",
      "rationale": "The module uses a compatible bracket-and-fastener architecture for frame joints, adhering to the specified criteria.",
      "evidence_ids": ["CURRENT-CAD"],
      "acceptance_check": "Visual inspection of the module's frame joints.",
      "risk": "None"
    },
    {
      "module_id": "BN-M09",
      "verdict": "RETAIN",
      "proposal": "Retain the current design.",
      "rationale": "The module uses a compatible bracket-and-fastener architecture for frame joints, adhering to the specified criteria.",
      "evidence_ids": ["CURRENT-CAD"],
      "acceptance_check": "Visual inspection of the module's frame joints.",
      "risk": "None"
    },
    {
      "module_id": "BN-M10",
      "verdict": "RETAIN",
      "proposal": "Retain the current design.",
      "rationale": "The module uses a compatible bracket-and-fastener architecture for frame joints, adhering to the specified criteria.",
      "evidence_ids": ["CURRENT-CAD"],
      "acceptance_check": "Visual inspection of the module's frame joints.",
      "risk": "None"
    }
  ]
}
```
