bagelboy137/Bear-Necessities-/Mac Mini Setup/tools/cad-product-agent/production/ten-modules/iterations/runs/manufacturing/manufacturing-05.attempt-1.raw.txt

```json
{
  "cycle_id": "manufacturing-05",
  "reviews": [
    {
      "module_id": "BN-M01",
      "verdict": "RETAIN",
      "proposal": "Retain current design.",
      "rationale": "Motion hardware standardization is not applicable as the module uses custom components.",
      "evidence_ids": ["CURRENT-CAD"],
      "acceptance_check": "Visual inspection of the module's motion hardware.",
      "risk": "None"
    },
    {
      "module_id": "BN-M02",
      "verdict": "RETAIN",
      "proposal": "Retain current design.",
      "rationale": "Motion hardware standardization is not applicable as the module uses custom components.",
      "evidence_ids": ["CURRENT-CAD"],
      "acceptance_check": "Visual inspection of the module's motion hardware.",
      "risk": "None"
    },
    {
      "module_id": "BN-M03",
      "verdict": "RETAIN",
      "proposal": "Retain current design.",
      "rationale": "Motion hardware standardization is not applicable as the module uses custom components.",
      "evidence_ids": ["CURRENT-CAD"],
      "acceptance_check": "Visual inspection of the module's motion hardware.",
      "risk": "None"
    },
    {
      "module_id": "BN-M04",
      "verdict": "RETAIN",
      "proposal": "Retain current design.",
      "rationale": "Motion hardware standardization is not applicable as the module uses custom components.",
      "evidence_ids": ["CURRENT-CAD"],
      "acceptance_check": "Visual inspection of the module's motion hardware.",
      "risk": "None"
    },
    {
      "module_id": "BN-M05",
      "verdict": "RETAIN",
      "proposal": "Retain current design.",
      "rationale": "Motion hardware standardization is not applicable as the module uses custom components.",
      "evidence_ids": ["CURRENT-CAD"],
      "acceptance_check": "Visual inspection of the module's motion hardware.",
      "risk": "None"
    },
    {
      "module_id": "BN-M06",
      "verdict": "RETAIN",
      "proposal": "Retain current design.",
      "rationale": "Motion hardware standardization is not applicable as the module uses custom components.",
      "evidence_ids": ["CURRENT-CAD"],
      "acceptance_check": "Visual inspection of the module's motion hardware.",
      "risk": "None"
    },
    {
      "module_id": "BN-M07",
      "verdict": "RETAIN",
      "proposal": "Retain current design.",
      "rationale": "Motion hardware standardization is not applicable as the module uses custom components.",
      "evidence_ids": ["CURRENT-CAD"],
      "acceptance_check": "Visual inspection of the module's motion hardware.",
      "risk": "None"
    },
    {
      "module_id": "BN-M08",
      "verdict": "RETAIN",
      "proposal": "Retain current design.",
      "rationale": "Motion hardware standardization is not applicable as the module uses custom components.",
      "evidence_ids": ["CURRENT-CAD"],
      "acceptance_check": "Visual inspection of the module's motion hardware.",
      "risk": "None"
    },
    {
      "module_id": "BN-M09",
      "verdict": "RETAIN",
      "proposal": "Retain current design.",
      "rationale": "Motion hardware standardization is not applicable as the module uses custom components.",
      "evidence_ids": ["CURRENT-CAD"],
      "acceptance_check": "Visual inspection of the module's motion hardware.",
      "risk": "None"
    },
    {
      "module_id": "BN-M10",
      "verdict": "RETAIN",
      "proposal": "Retain current design.",
      "rationale": "Motion hardware standardization is not applicable as the module uses custom components.",
      "evidence_ids": ["CURRENT-CAD"],
      "acceptance_check": "Visual inspection of the module's motion hardware.",
      "risk": "None"
    }
  ]
}
```
