bagelboy137/Bear-Necessities-/Mac Mini Setup/tools/cad-product-agent/production/ten-modules/iterations/runs/manufacturing/manufacturing-08.attempt-1.raw.txt

```json
{
  "cycle_id": "manufacturing-08",
  "reviews": [
    {
      "module_id": "BN-M01",
      "verdict": "RETAIN",
      "proposal": "Retain current design.",
      "rationale": "The tolerance and clearance for the cook station are within acceptable limits based on the current CAD design.",
      "evidence_ids": ["CURRENT-CAD"],
      "acceptance_check": "Visual inspection of the CAD model for proper clearances.",
      "risk": "None"
    },
    {
      "module_id": "BN-M02",
      "verdict": "RETAIN",
      "proposal": "Retain current design.",
      "rationale": "The tolerance and clearance for the dry pantry are within acceptable limits based on the current CAD design.",
      "evidence_ids": ["CURRENT-CAD"],
      "acceptance_check": "Visual inspection of the CAD model for proper clearances.",
      "risk": "None"
    },
    {
      "module_id": "BN-M03",
      "verdict": "RETAIN",
      "proposal": "Retain current design.",
      "rationale": "The tolerance and clearance for the fridge freezer are within acceptable limits based on the current CAD design.",
      "evidence_ids": ["CURRENT-CAD"],
      "acceptance_check": "Visual inspection of the CAD model for proper clearances.",
      "risk": "None"
    },
    {
      "module_id": "BN-M04",
      "verdict": "RETAIN",
      "proposal": "Retain current design.",
      "rationale": "The tolerance and clearance for the sink wash are within acceptable limits based on the current CAD design.",
      "evidence_ids": ["CURRENT-CAD"],
      "acceptance_check": "Visual inspection of the CAD model for proper clearances.",
      "risk": "None"
    },
    {
      "module_id": "BN-M05",
      "verdict": "RETAIN",
      "proposal": "Retain current design.",
      "rationale": "The tolerance and clearance for the fresh water are within acceptable limits based on the current CAD design.",
      "evidence_ids": ["CURRENT-CAD"],
      "acceptance_check": "Visual inspection of the CAD model for proper clearances.",
      "risk": "None"
    },
    {
      "module_id": "BN-M06",
      "verdict": "RETAIN",
      "proposal": "Retain current design.",
      "rationale": "The tolerance and clearance for the recovery utility are within acceptable limits based on the current CAD design.",
      "evidence_ids": ["CURRENT-CAD"],
      "acceptance_check": "Visual inspection of the CAD model for proper clearances.",
      "risk": "None"
    },
    {
      "module_id": "BN-M07",
      "verdict": "RETAIN",
      "proposal": "Retain current design.",
      "rationale": "The tolerance and clearance for the power hub are within acceptable limits based on the current CAD design.",
      "evidence_ids": ["CURRENT-CAD"],
      "acceptance_check": "Visual inspection of the CAD model for proper clearances.",
      "risk": "None"
    },
    {
      "module_id": "BN-M08",
      "verdict": "RETAIN",
      "proposal": "Retain current design.",
      "rationale": "The tolerance and clearance for the hot water shower are within acceptable limits based on the current CAD design.",
      "evidence_ids": ["CURRENT-CAD"],
      "acceptance_check": "Visual inspection of the CAD model for proper clearances.",
      "risk": "None"
    },
    {
      "module_id": "BN-M09",
      "verdict": "RETAIN",
      "proposal": "Retain current design.",
      "rationale": "The tolerance and clearance for the field office camera are within acceptable limits based on the current CAD design.",
      "evidence_ids": ["CURRENT-CAD"],
      "acceptance_check": "Visual inspection of the CAD model for proper clearances.",
      "risk": "None"
    },
    {
      "module_id": "BN-M10",
      "verdict": "RETAIN",
      "proposal": "Retain current design.",
      "rationale": "The tolerance and clearance for the camp furniture soft goods are within acceptable limits based on the current CAD design.",
      "evidence_ids": ["CURRENT-CAD"],
      "acceptance_check": "Visual inspection of the CAD model for proper clearances.",
      "risk": "None"
    }
  ]
}
```
