bagelboy137/Bear-Necessities-/Mac Mini Setup/tools/cad-product-agent/production/ten-modules/iterations/runs/manufacturing/manufacturing-09.attempt-2.raw.txt

```json
{
  "cycle_id": "manufacturing-09",
  "reviews": [
    {
      "module_id": "BN-M01",
      "verdict": "RETAIN",
      "proposal": "Retain current design.",
      "rationale": "BN-M01 is not a sold-out item and meets all requirements.",
      "evidence_ids": ["8020-3393", "8020-4132"],
      "acceptance_check": "Confirm no changes are needed for BN-M01.",
      "risk": "None."
    },
    {
      "module_id": "BN-M02",
      "verdict": "RETAIN",
      "proposal": "Retain current design.",
      "rationale": "BN-M02 is not a sold-out item and meets all requirements.",
      "evidence_ids": ["8020-3393", "8020-4132"],
      "acceptance_check": "Confirm no changes are needed for BN-M02.",
      "risk": "None."
    },
    {
      "module_id": "BN-M03",
      "verdict": "REVISE",
      "proposal": "Replace with alternate procurement for sold-out item.",
      "rationale": "BN-M03 is a sold-out primary product with an alternate procurement available.",
      "evidence_ids": ["ENGEL-MD14", "ENGEL-MHD13-ALT"],
      "acceptance_check": "Verify alternate procurement is available and meets specifications.",
      "risk": "Ensure compatibility with existing design and functionality."
    },
    {
      "module_id": "BN-M04",
      "verdict": "RETAIN",
      "proposal": "Retain current design.",
      "rationale": "BN-M04 is not a sold-out item and meets all requirements.",
      "evidence_ids": ["DOMETIC-VA8005"],
      "acceptance_check": "Confirm no changes are needed for BN-M04.",
      "risk": "None."
    },
    {
      "module_id": "BN-M05",
      "verdict": "RETAIN",
      "proposal": "Retain current design.",
      "rationale": "BN-M05 is not a sold-out item and meets all requirements.",
      "evidence_ids": ["RELIANCE-AQUATAINER-7G"],
      "acceptance_check": "Confirm no changes are needed for BN-M05.",
      "risk": "None."
    },
    {
      "module_id": "BN-M06",
      "verdict": "RETAIN",
      "proposal": "Retain current design.",
      "rationale": "BN-M06 is not a sold-out item and meets all requirements.",
      "evidence_ids": ["PELICAN-1450"],
      "acceptance_check": "Confirm no changes are needed for BN-M06.",
      "risk": "None."
    },
    {
      "module_id": "BN-M07",
      "verdict": "RETAIN",
      "proposal": "Retain current design.",
      "rationale": "BN-M07 is not a sold-out item and meets all requirements.",
      "evidence_ids": ["ECOFLOW-RIVER3-PLUS"],
      "acceptance_check": "Confirm no changes are needed for BN-M07.",
      "risk": "None."
    },
    {
      "module_id": "BN-M08",
      "verdict": "RETAIN",
      "proposal": "Retain current design.",
      "rationale": "BN-M08 is not a sold-out item and meets all requirements.",
      "evidence_ids": ["JOOLCA-HOTTAP-V2"],
      "acceptance_check": "Confirm no changes are needed for BN-M08.",
      "risk": "None."
    },
    {
      "module_id": "BN-M09",
      "verdict": "RETAIN",
      "proposal": "Retain current design.",
      "rationale": "BN-M09 is not a sold-out item and meets all requirements.",
      "evidence_ids": ["PELICAN-1485"],
      "acceptance_check": "Confirm no changes are needed for BN-M09.",
      "risk": "None."
    },
    {
      "module_id": "BN-M10",
      "verdict": "RETAIN",
      "proposal": "Retain current design.",
      "rationale": "BN-M10 is not a sold-out item and meets all requirements.",
      "evidence_ids": ["HELINOX-CHAIR-ONE", "HELINOX-TABLE-ONE"],
      "acceptance_check": "Confirm no changes are needed for BN-M10.",
      "risk": "None."
    }
  ]
}
```
