bagelboy137/Bear-Necessities-/Mac Mini Setup/tools/cad-product-agent/production/ten-modules/fusion-native/exports/BN-M01/BN-M01-iso.png

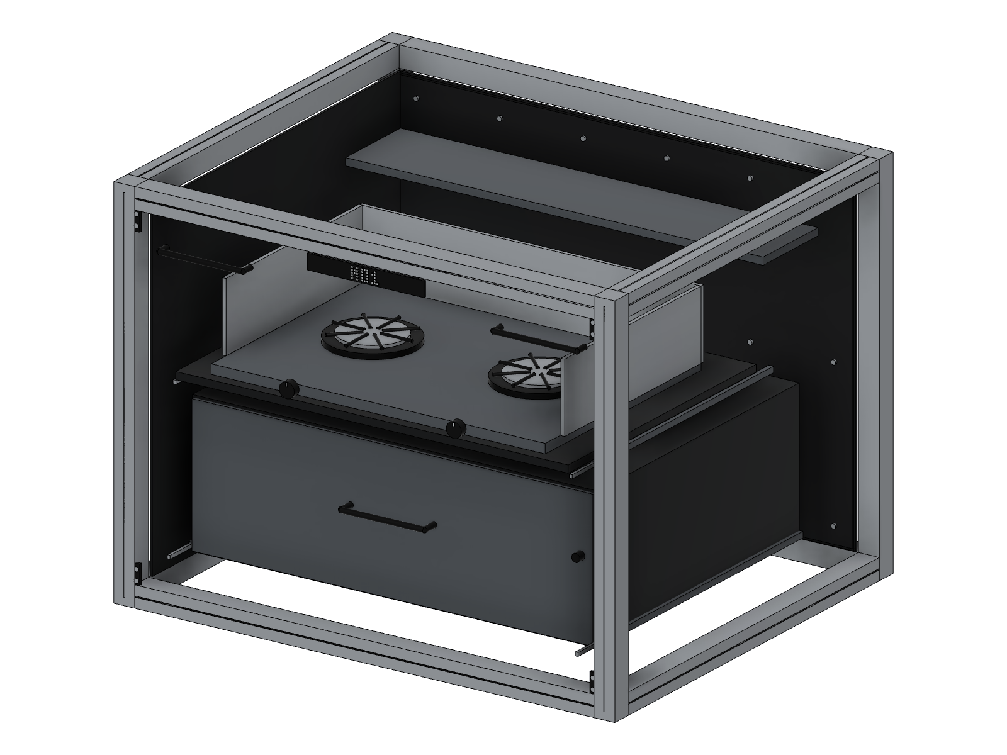
Mac Mini Setup/tools/cad-product-agent/production/ten-modules/fusion-native/exports/BN-M01/BN-M01-iso.png
