bagelboy137/Bear-Necessities-/Mac Mini Setup/tools/cad-product-agent/production/ten-modules/fusion-native/exports/BN-M02/BN-M02-front.png

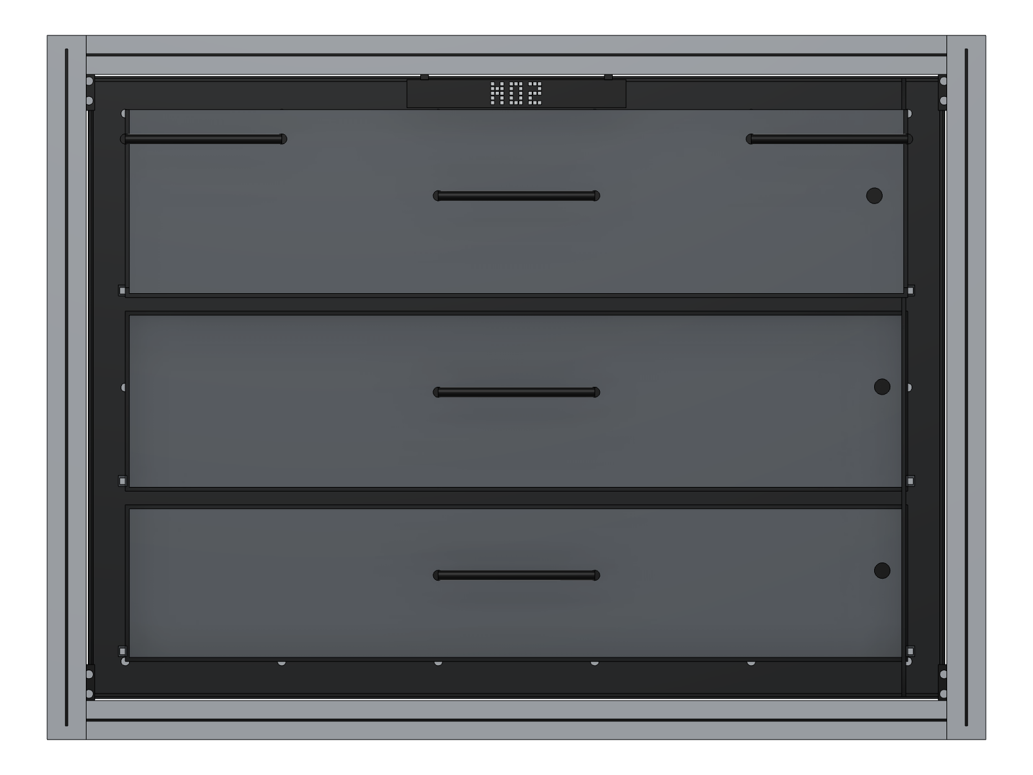
Mac Mini Setup/tools/cad-product-agent/production/ten-modules/fusion-native/exports/BN-M02/BN-M02-front.png
